leonardoAB1/smoke_detector_camera/docs/inform/media/markiv/simulacion_base_.png

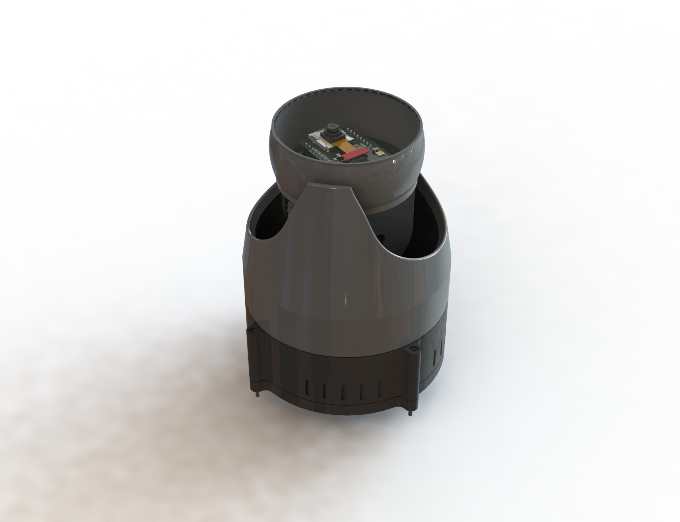
docs/inform/media/markiv/simulacion_base_.png
