leonardoAB1/smoke_detector_camera/docs/inform/media/vista_explosionada_mark3.png

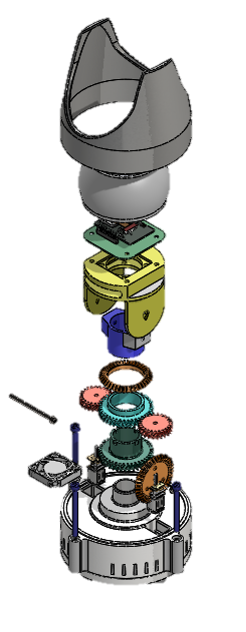
docs/inform/media/vista_explosionada_mark3.png
