leonardoAB1/smoke_detector_camera/cad/mark_02/components/LightSensor.step

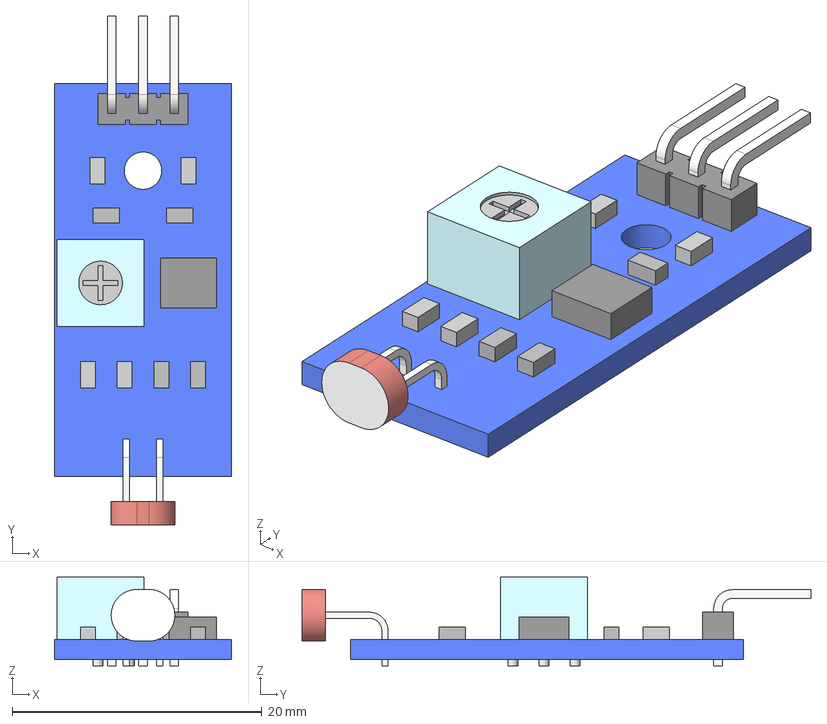
[picture p47: CAD file, 2023-06-11]
cad/mark_02/components/LightSensor.step
14.2 x 40.8 x 7.10 mm
