leonardoAB1/smoke_detector_camera/cad/mark_02/components/MQ135.SLDPRT

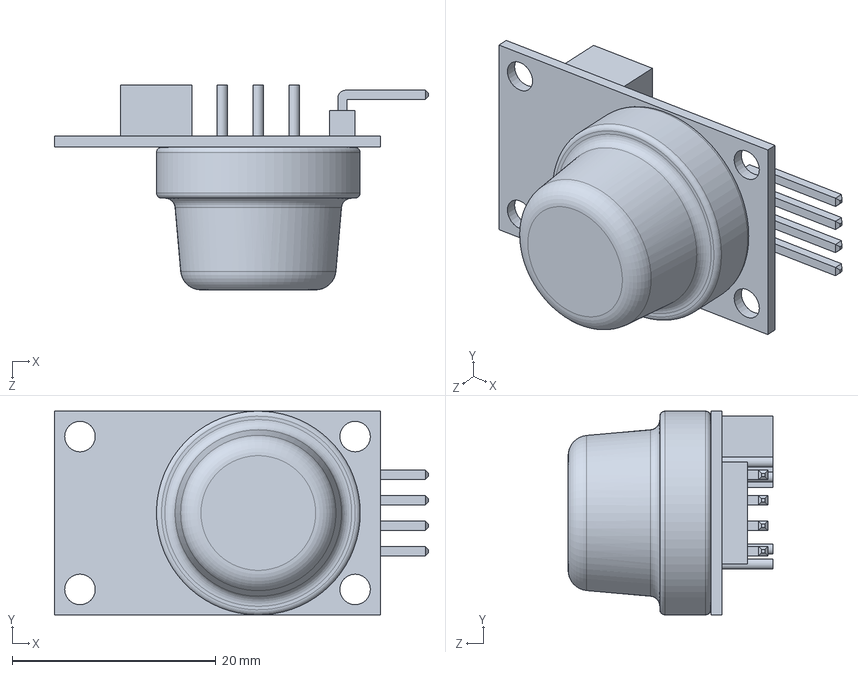
[picture p48: CAD file, 2023-06-11]
cad/mark_02/components/MQ135.SLDPRT
36.7 x 20.0 x 20.1 mm
