leonardoAB1/smoke_detector_camera/cad/mark_02/components/Li-Ion_Cell_Holder_BH_18650_A.SLDPRT

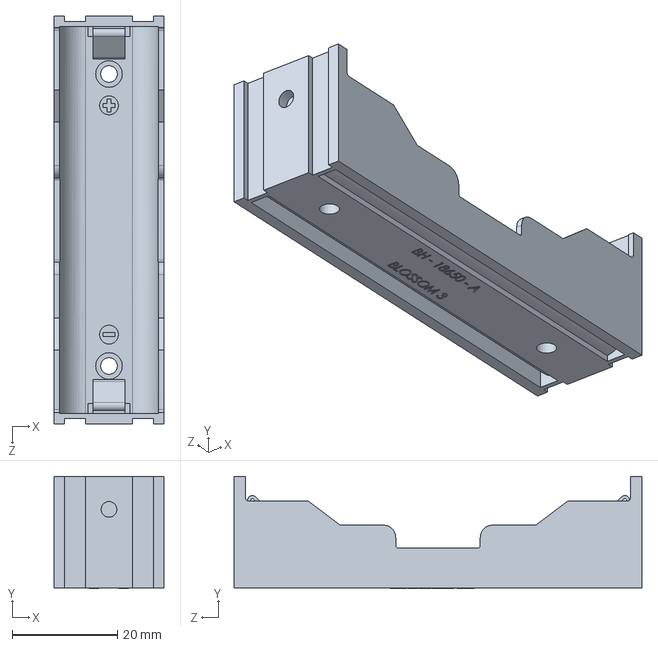
[picture p49: CAD file, 2023-06-11]
cad/mark_02/components/Li-Ion_Cell_Holder_BH_18650_A.SLDPRT
20.9 x 21.4 x 77.7 mm
