leonardoAB1/smoke_detector_camera/cad/mark_02/components/PIR-HC_SR501.SLDPRT

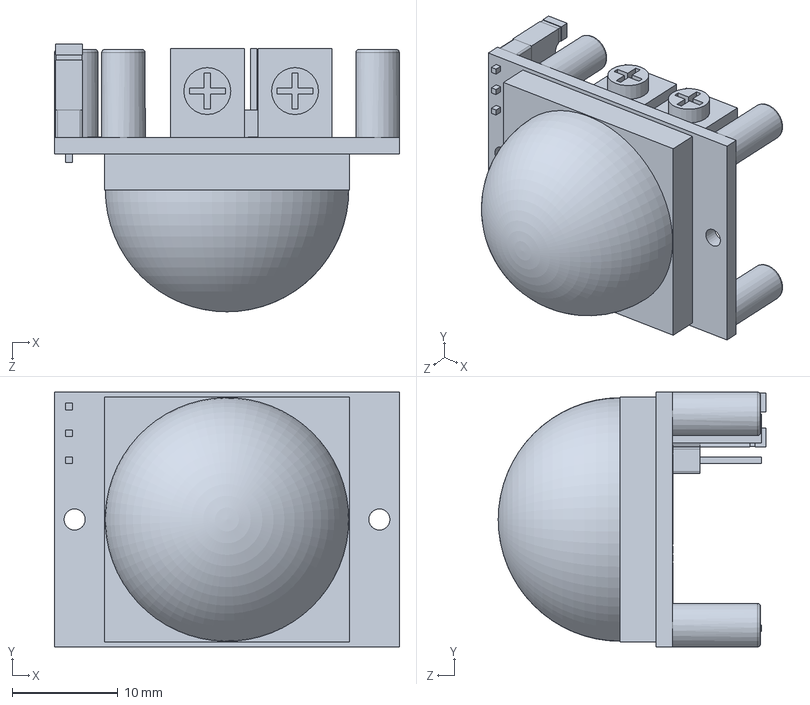
[picture p50: CAD file, 2023-06-11]
cad/mark_02/components/PIR-HC_SR501.SLDPRT
32.6 x 24.1 x 25.3 mm
