leonardoAB1/smoke_detector_camera/cad/mark_02/components/MG995.SLDPRT

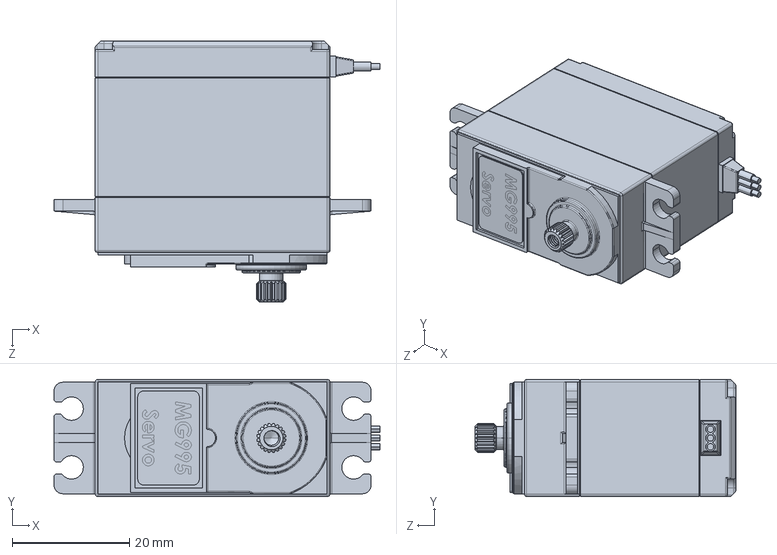
[picture p51: CAD file, 2023-06-11]
cad/mark_02/components/MG995.SLDPRT
55.5 x 20.0 x 44.5 mm
