leonardoAB1/smoke_detector_camera/cad/mark_02/components/Microservo horn.SLDPRT

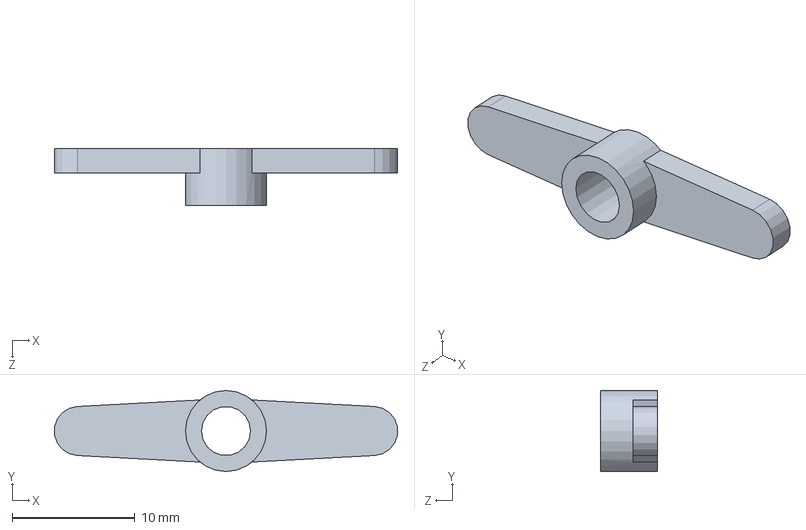
[picture p52: CAD file, 2023-06-11]
cad/mark_02/components/Microservo horn.SLDPRT
27.9 x 6.60 x 4.68 mm
