leonardoAB1/smoke_detector_camera/cad/mark_02/components/ELCOM EMI-21 INLET 16 amps.STEP

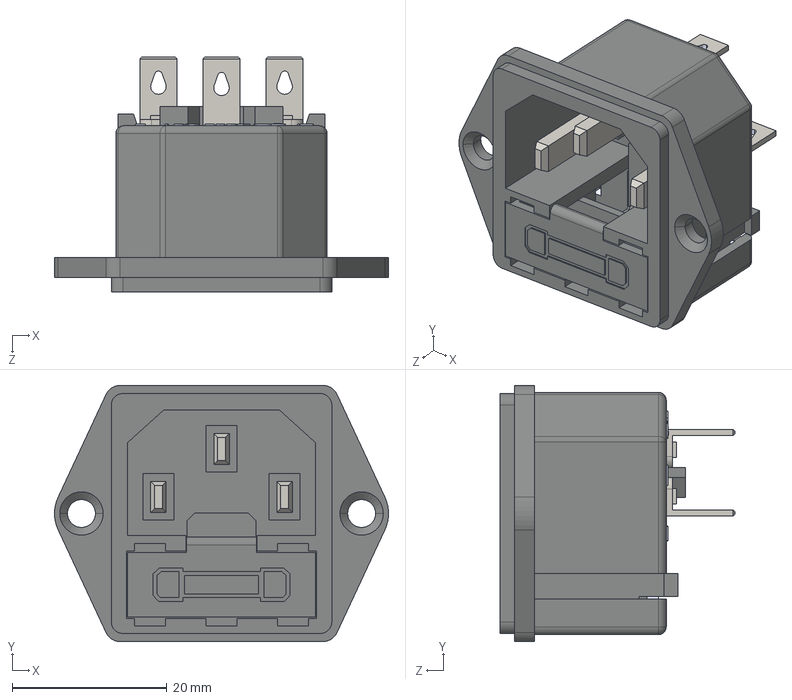
[picture p53: CAD file, 2023-06-11]
cad/mark_02/components/ELCOM EMI-21 INLET 16 amps.STEP
43.2 x 33.1 x 30.4 mm
ELCOM EMI-21 INLET
ELCOM EMI-21 INLET tray
