leonardoAB1/smoke_detector_camera/cad/mark_02/components/Switch.SLDPRT

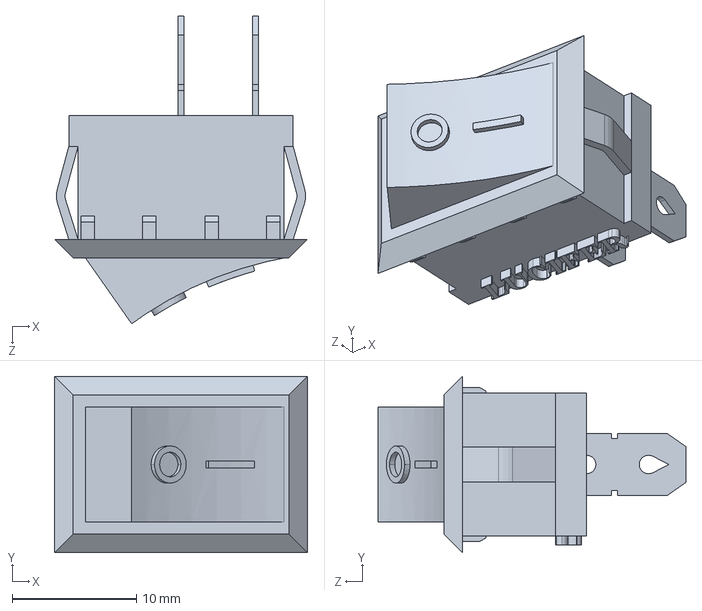
[picture p54: CAD file, 2023-06-09]
cad/mark_02/components/Switch.SLDPRT
20.4 x 14.2 x 24.8 mm
