leonardoAB1/smoke_detector_camera/cad/mark_02/components/MG90S.SLDPRT

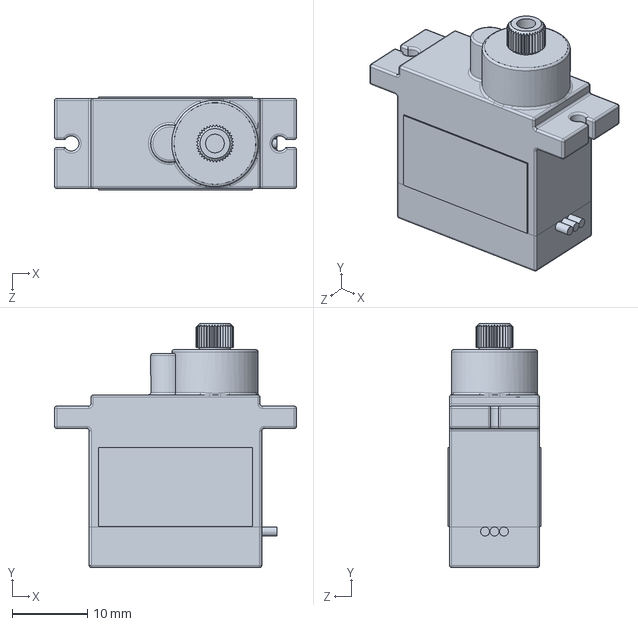
[picture p55: CAD file, 2023-06-02]
cad/mark_02/components/MG90S.SLDPRT
32.2 x 32.5 x 12.4 mm
