leonardoAB1/smoke_detector_camera/src/device/main/src/http_handlers/http_handlers.c

/*******************************************************************************
 * @file        http_handlers.c
 * @author      Leonardo Acha Boiano
 * @date        7 Jun 2023
 * 
 * @note        This code is written in C and is used on an ESP32-CAM development board.
 *
 *******************************************************************************/

#include "../http_handlers/http_handlers.h"

// HTTP request handler for getting a single image base64 encoded
esp_err_t image_base64_httpd_handler(httpd_req_t *req)
{
    // Authenticate the user
    authenticatedUserRole = authenticateUser(req);

    if (authenticatedUserRole != ROLE_USER && authenticatedUserRole != ROLE_ADMIN) {
        httpd_resp_send_err(req, HTTPD_401_UNAUTHORIZED, "Unauthorized");
        return ESP_OK;
    }

    camera_fb_t *fb = esp_camera_fb_get();
    if (!fb) {
        ESP_LOGE(CAMERA_TAG, "Camera capture failed");
        httpd_resp_send_err(req, HTTPD_500_INTERNAL_SERVER_ERROR, "Internal Server Error");
        return ESP_FAIL;
    }

    // Set the content type header
    httpd_resp_set_type(req, "image/jpeg");

    // Calculate the size of the base64-encoded data
    size_t encoded_len = (fb->len + 2) / 3 * 4;

    char *encoded_data = (char *)malloc(encoded_len);
    if (!encoded_data) {
        ESP_LOGE(CAMERA_TAG, "Memory allocation failed");
        httpd_resp_send_err(req, HTTPD_500_INTERNAL_SERVER_ERROR, "Internal Server Error");
        esp_camera_fb_return(fb);
        return ESP_FAIL;
    }

    // Encode the image data using base64
    size_t encoded_data_len = encoded_len;
    int ret = base64_encode((const unsigned char *)fb->buf, fb->len, encoded_data, &encoded_data_len);
    if (ret != 0) {
        ESP_LOGE(CAMERA_TAG, "Base64 encoding failed. Error code: %d", ret);
        ESP_LOGE(CAMERA_TAG, "Encoded data length: %d", encoded_data_len);
        httpd_resp_send_err(req, HTTPD_500_INTERNAL_SERVER_ERROR, "Internal Server Error");
        free(encoded_data);
        esp_camera_fb_return(fb);
        return ESP_FAIL;
    }

    // Send the encoded image data as the response
    httpd_resp_send(req, encoded_data, encoded_data_len);

    // Cleanup
    free(encoded_data);
    esp_camera_fb_return(fb);

    return ESP_OK;
}

// HTTP request handler for getting a single image
esp_err_t image_httpd_handler(httpd_req_t *req)
{
    // Authenticate the user
    authenticatedUserRole = authenticateUser(req);

    if (authenticatedUserRole != ROLE_USER && authenticatedUserRole != ROLE_ADMIN) {
        httpd_resp_send_err(req, HTTPD_401_UNAUTHORIZED, "Unauthorized");
        return ESP_OK;
    }

    camera_fb_t *fb = esp_camera_fb_get();
    if (!fb) {
        ESP_LOGE(CAMERA_TAG, "Camera capture failed");
        httpd_resp_send_err(req, HTTPD_500_INTERNAL_SERVER_ERROR, "Internal Server Error");
        return ESP_FAIL;
    }

    // Set the content type header
    httpd_resp_set_type(req, "image/jpeg");

    // Send the image data
    httpd_resp_send(req, (const char *)fb->buf, fb->len);

    esp_camera_fb_return(fb);
    return ESP_OK;
}

// HTTP request handler for getting the camera status
esp_err_t status_httpd_handler(httpd_req_t *req)
{
    // Authenticate the user
    authenticatedUserRole = authenticateUser(req);

    if (authenticatedUserRole != ROLE_USER && authenticatedUserRole != ROLE_ADMIN) {
        httpd_resp_send_err(req, HTTPD_401_UNAUTHORIZED, "Unauthorized");
        return ESP_OK;
    }

    cJSON *root = cJSON_CreateObject();
    cJSON_AddStringToObject(root, "status", "online");

    char *response = cJSON_Print(root);

    httpd_resp_set_type(req, "application/json");
    httpd_resp_send(req, response, strlen(response));

    cJSON_Delete(root);
    free(response);

    return ESP_OK;
}

// HTTP request handler for admin functionality
esp_err_t admin_httpd_handler(httpd_req_t *req)
{
    // Authenticate the user
    authenticatedUserRole = authenticateUser(req);

    if (authenticatedUserRole != ROLE_ADMIN) {
        httpd_resp_send_err(req, HTTPD_401_UNAUTHORIZED, "Unauthorized");
        return ESP_OK;
    }

    // Check if the request method is POST
    if (req->method != HTTP_POST) {
        httpd_resp_send_err(req, HTTPD_405_METHOD_NOT_ALLOWED, "Method Not Allowed");
        return ESP_OK;
    }

    // Get the content length
    char content_length_str[16];
    if (httpd_req_get_hdr_value_str(req, "Content-Length", content_length_str, sizeof(content_length_str)) != ESP_OK) {
        httpd_resp_send_err(req, HTTPD_400_BAD_REQUEST, "Bad Request");
        return ESP_OK;
    }

    size_t content_len = atoi(content_length_str);

    // Read the request content data
    char *content = malloc(content_len + 1);
    if (!content) {
        httpd_resp_send_err(req, HTTPD_500_INTERNAL_SERVER_ERROR, "Internal Server Error");
        return ESP_OK;
    }

    int ret = httpd_req_recv(req, content, content_len);
    if (ret <= 0) {
        free(content);
        httpd_resp_send_err(req, HTTPD_400_BAD_REQUEST, "Bad Request");
        return ESP_OK;
    }

    content[ret] = '\0'; // Null-terminate the content

    // Parse the JSON content
    cJSON *json = cJSON_Parse(content);
    if (!json) {
        free(content);
        httpd_resp_send_err(req, HTTPD_400_BAD_REQUEST, "Invalid JSON");
        return ESP_OK;
    }

    // Get the value from the JSON object
    cJSON *valueObj = cJSON_GetObjectItem(json, "value");
    if (!valueObj || !cJSON_IsNumber(valueObj)) {
        cJSON_Delete(json);
        free(content);
        httpd_resp_send_err(req, HTTPD_400_BAD_REQUEST, "Invalid JSON");
        return ESP_OK;
    }

    int value = valueObj->valueint;

    // Log the updated value
    ESP_LOGI(ADMIN_TAG, "Value updated: %d", value);

    // Process the value (e.g., perform admin action)
    // ...

    // Cleanup
    cJSON_Delete(json);
    free(content);

    // Send a response
    httpd_resp_set_type(req, "text/plain");
    httpd_resp_send(req, "Value updated successfully", -1);

    return ESP_OK;
}

// Handler for the API endpoint to control the motors
esp_err_t handle_set_motor_angle(httpd_req_t *req) {
    // Authenticate the user and check if the role is admin
    authenticatedUserRole = authenticateUser(req);
    if (authenticatedUserRole != ROLE_ADMIN) {
        // Return an error response indicating insufficient permissions
        httpd_resp_send_err(req, HTTPD_401_UNAUTHORIZED, "Insufficient permissions");
        return ESP_OK;
    }

    // TODO:Extract the desired motor angles from the request parameters
    // Example: int angle1 = extract_angle_from_request(req, "angle1");
    //          int angle2 = extract_angle_from_request(req, "angle2");
    
    // Call the move_motors_custom() function to move the motors accordingly
    // Example: move_motors_custom(angle1, angle2);
    
    // Return a success response indicating the motors have been moved
    httpd_resp_sendstr(req, "Motors moved successfully");
    return ESP_OK;
}

// Handler for the API endpoint to get the motor current position
esp_err_t handle_get_motor_angle(httpd_req_t *req)
{
    // Authenticate the user and check if the role is admin or user
    authenticatedUserRole = authenticateUser(req);
    if (authenticatedUserRole == ROLE_UNKNOWN)
    {
        // Return an error response indicating unauthorized access
        httpd_resp_send_err(req, HTTPD_401_UNAUTHORIZED, "Unauthorized access");
        return ESP_OK;
    }

    // Get the motor number from the request header
    int motorNumber = -1;
    size_t motorHeaderLen = httpd_req_get_hdr_value_len(req, "Motor-Number");
    if (motorHeaderLen > 0)
    {
        char *motorHeader = malloc(motorHeaderLen + 1);
        httpd_req_get_hdr_value_str(req, "Motor-Number", motorHeader, motorHeaderLen + 1);
        motorNumber = atoi(motorHeader);
        free(motorHeader);
    }

    // Check the motor number and retrieve the corresponding motor angle
    float motorAngle = -1.0;
    if (motorNumber == 1)
    {
        motorAngle = get_motor_angle(&motor1);
    }
    else if (motorNumber == 2)
    {
        motorAngle = get_motor_angle(&motor2);
    }
    else
    {
        // Return an error response for an invalid motor number
        httpd_resp_send_err(req, HTTPD_400_BAD_REQUEST, "Invalid motor number");
        return ESP_OK;
    }

    // Create a JSON response payload with the motor angle
    cJSON *json = cJSON_CreateObject();
    cJSON_AddNumberToObject(json, "motor_angle", motorAngle);
    char *payload = cJSON_PrintUnformatted(json);
    cJSON_Delete(json);

    // Set the Content-Type header to application/json
    httpd_resp_set_type(req, "application/json");

    // Send the JSON response payload
    httpd_resp_send(req, payload, strlen(payload));

    // Free the allocated JSON payload
    free(payload);

    return ESP_OK;
}

// Handler for the API endpoint to control the LEDs
esp_err_t handle_set_ldr(httpd_req_t *req) {
    // Authenticate the user and check if the role is admin
    authenticatedUserRole = authenticateUser(req);
    if (authenticatedUserRole != ROLE_ADMIN) {
        // Return an error response indicating insufficient permissions
        httpd_resp_send_err(req, HTTPD_401_UNAUTHORIZED, "Insufficient permissions");
        return ESP_OK;
    }

    // TODO:Extract the desired LED state from the request parameters
    // Example: bool ledState = extract_led_state_from_request(req, "ledState");
    
    // Set the LED GPIO pin state accordingly
    // Example: gpio_set_level(GPIO_LEDS, ledState);
    
    // Return a success response indicating the LEDs have been controlled
    httpd_resp_sendstr(req, "LDR controlled successfully");
    return ESP_OK;
}

// Handler for the API endpoint to get the LEDs current state
esp_err_t handle_get_ldr(httpd_req_t *req){
    // Authenticate the user and check if the role is admin or user
    authenticatedUserRole = authenticateUser(req);
    if (authenticatedUserRole == ROLE_UNKNOWN) {
        // Return an error response indicating unauthorized access
        httpd_resp_send_err(req, HTTPD_401_UNAUTHORIZED, "Unauthorized access");
        return ESP_OK;
    }

    // Prepare the response JSON
    cJSON *root = cJSON_CreateObject();
    cJSON_AddStringToObject(root, "state", getLdrState() == 0 ? "0" : "1");

    char *response = cJSON_Print(root);

    // Set the response headers and send the response
    httpd_resp_set_type(req, "application/json");
    httpd_resp_send(req, response, strlen(response));

    // Clean up
    cJSON_Delete(root);
    free(response);

    return ESP_OK;
}



// Handler for the API endpoint to control the LEDs
esp_err_t handle_set_led(httpd_req_t *req) {
    // Authenticate the user and check if the role is admin
    authenticatedUserRole = authenticateUser(req);
    if (authenticatedUserRole != ROLE_ADMIN) {
        // Return an error response indicating insufficient permissions
        httpd_resp_send_err(req, HTTPD_401_UNAUTHORIZED, "Insufficient permissions");
        return ESP_OK;
    }

    // TODO:Extract the desired LED state from the request parameters
    // Example: bool ledState = extract_led_state_from_request(req, "ledState");
    
    // Set the LED GPIO pin state accordingly
    // Example: gpio_set_level(GPIO_LEDS, ledState);
    
    // Return a success response indicating the LEDs have been controlled
    httpd_resp_sendstr(req, "LEDs controlled successfully");
    return ESP_OK;
}

// Handler for the API endpoint to get the LEDs current state
esp_err_t handle_get_led(httpd_req_t *req){
    // Authenticate the user and check if the role is admin or user
    authenticatedUserRole = authenticateUser(req);
    if (authenticatedUserRole == ROLE_UNKNOWN) {
        // Return an error response indicating unauthorized access
        httpd_resp_send_err(req, HTTPD_401_UNAUTHORIZED, "Unauthorized access");
        return ESP_OK;
    }

    // Prepare the response JSON
    cJSON *root = cJSON_CreateObject();
    cJSON_AddStringToObject(root, "state", getLedState() == 0 ? "0" : "1");

    char *response = cJSON_Print(root);

    // Set the response headers and send the response
    httpd_resp_set_type(req, "application/json");
    httpd_resp_send(req, response, strlen(response));

    // Clean up
    cJSON_Delete(root);
    free(response);

    return ESP_OK;
}

// Handler for the API endpoint to set the smoke sensor test variable
// Implemented in order to test system behavior
esp_err_t handle_set_smoke_sensor(httpd_req_t *req){
    // Authenticate the user and check if the role is admin
    authenticatedUserRole = authenticateUser(req);
    if (authenticatedUserRole != ROLE_ADMIN) {
        // Return an error response indicating insufficient permissions
        httpd_resp_send_err(req, HTTPD_401_UNAUTHORIZED, "Insufficient permissions");
        return ESP_OK;
    }

    //TODO: Implement handler

    return ESP_OK;
}

// Handler for the API endpoint to access the smoke sensor data
esp_err_t handle_get_smoke_sensor(httpd_req_t *req) {
    // Authenticate the user and check if the role is admin or user
    authenticatedUserRole = authenticateUser(req);
    if (authenticatedUserRole == ROLE_UNKNOWN) {
        // Return an error response indicating unauthorized access
        httpd_resp_send_err(req, HTTPD_401_UNAUTHORIZED, "Unauthorized access");
        return ESP_OK;
    }
    
    // Return the JSON response
    cJSON *root = cJSON_CreateObject();
    cJSON_AddStringToObject(root, "state", getSmokeSensorState() == 0 ? "0" : "1");

    char *response = cJSON_Print(root);

    // Set the response headers and send the response
    httpd_resp_set_type(req, "application/json");
    httpd_resp_send(req, response, strlen(response));

    // Clean up
    cJSON_Delete(root);
    free(response);

    return ESP_OK;
}

/********************************* END OF FILE ********************************/
/******************************************************************************/
