leonardoAB1/smoke_detector_camera/src/device/main/src/http_handlers/http_handlers.h

/*******************************************************************************
 * @file        http_handlers.h
 * @brief       Header file containing declarations of HTTP request handlers.
 * @author      Leonardo Acha Boiano
 * @date        7 Jun 2023
 * 
 * @note        This code is written in C and is used on an ESP32-CAM development board.
 *
 *******************************************************************************/

#ifndef HTTP_HANDLERS_H
#define HTTP_HANDLERS_H

#include <stdio.h>
#include <stdlib.h>
#include <string.h>
#include <esp_log.h>
#include <esp_camera.h>
#include <cJSON.h>
#include <esp_http_server.h>

#include "../logging/logging_utils.h"
#include "../user_roles/user_roles.h"
#include "../base64/base64_utils.h"
#include "../camera/camera_pins.h"
#include "../gpio_interrupts/gpio_interrupts.h"
#include "../gpio_state/gpio_state.h"
#include "../motor_control/motor_control.h"

/**
 * @brief       The authenticated user role.
 * @note        This variable is defined in main.c.
 */
extern UserRole authenticatedUserRole;

/**
 * @brief       HTTP request handler for getting a single image in base64 encoding.
 * @param[in]   req The HTTP request object.
 * @return      An esp_err_t indicating the success or failure of the operation.
 */
esp_err_t image_base64_httpd_handler(httpd_req_t *req);

/**
 * @brief       HTTP request handler for getting a single image.
 * @param[in]   req The HTTP request object.
 * @return      An esp_err_t indicating the success or failure of the operation.
 */
esp_err_t image_httpd_handler(httpd_req_t *req);

/**
 * @brief       HTTP request handler for getting the camera status.
 * @param[in]   req The HTTP request object.
 * @return      An esp_err_t indicating the success or failure of the operation.
 */
esp_err_t status_httpd_handler(httpd_req_t *req);

/**
 * @brief       HTTP request handler for admin functionality.
 * @param[in]   req The HTTP request object.
 * @return      An esp_err_t indicating the success or failure of the operation.
 */
esp_err_t admin_httpd_handler(httpd_req_t *req);

esp_err_t handle_set_motor_angle(httpd_req_t *req); //motor number and angle needed in header
esp_err_t handle_get_motor_angle(httpd_req_t *req);
esp_err_t handle_set_ldr(httpd_req_t *req);
esp_err_t handle_get_ldr(httpd_req_t *req);
esp_err_t handle_set_led(httpd_req_t *req);
esp_err_t handle_get_led(httpd_req_t *req);
esp_err_t handle_set_smoke_sensor(httpd_req_t *req);
esp_err_t handle_get_smoke_sensor(httpd_req_t *req);

extern Motor motor1;
extern Motor motor2;

#endif  // HTTP_HANDLERS_H

/********************************* END OF FILE ********************************/
/******************************************************************************/
