leonardoAB1/smoke_detector_camera/src/device/main/src/bt_utils/bt_utils.c

/*******************************************************************************
 * @file        bt_utils.c
 * @author      Leonardo Acha Boiano
 * @date        20 Jul 2023
 * 
 * @note        This code is written in C and is used on an ESP32-CAM development board.
 *
 *******************************************************************************/

#include "../bt_utils/bt_utils.h"

#if ENABLE_BT

static uint32_t connection_handle;

static const esp_spp_mode_t esp_spp_mode = ESP_SPP_MODE_CB;
static const bool esp_spp_enable_l2cap_ertm = true;

static struct timeval time_new, time_old;
static long data_num = 0;

static const esp_spp_sec_t sec_mask = ESP_SPP_SEC_AUTHENTICATE;
static const esp_spp_role_t role_slave = ESP_SPP_ROLE_SLAVE;

void bt_printf(const char *format, ...)
{
    // Check if the connection handle is valid
    if (connection_handle == NULL) {
        printf("Bluetooth connection handle is not valid. Cannot send data.\n");
        return;
    }

    // Create a buffer to hold the formatted string
    char buffer[BT_TX_BUFFER_SIZE];

    // Format the string using variable arguments
    va_list args;
    va_start(args, format);
    vsnprintf(buffer, sizeof(buffer), format, args);
    va_end(args);

    // Print the formatted string to the console for debugging (optional)
    //printf("Formatted string: %s", buffer);

    // Send the formatted string through Bluetooth
    esp_spp_write(connection_handle, strlen(buffer), (uint8_t *)buffer);
}

static char *bda2str(uint8_t * bda, char *str, size_t size)
{
    if (bda == NULL || str == NULL || size < 18) {
        return NULL;
    }

    uint8_t *p = bda;
    sprintf(str, "%02x:%02x:%02x:%02x:%02x:%02x",
            p[0], p[1], p[2], p[3], p[4], p[5]);
    return str;
}

static void print_speed(void)
{
    float time_old_s = time_old.tv_sec + time_old.tv_usec / 1000000.0;
    float time_new_s = time_new.tv_sec + time_new.tv_usec / 1000000.0;
    float time_interval = time_new_s - time_old_s;
    float speed = data_num * 8 / time_interval / 1000.0;
    ESP_LOGI(BT_TAG, "speed(%fs ~ %fs): %f kbit/s" , time_old_s, time_new_s, speed);
    data_num = 0;
    time_old.tv_sec = time_new.tv_sec;
    time_old.tv_usec = time_new.tv_usec;
}

static void esp_spp_cb(esp_spp_cb_event_t event, esp_spp_cb_param_t *param)
{
    char bda_str[18] = {0};

    switch (event) {
    case ESP_SPP_INIT_EVT:
        if (param->init.status == ESP_SPP_SUCCESS) {
            ESP_LOGI(BT_TAG, "ESP_SPP_INIT_EVT");
            esp_spp_start_srv(sec_mask, role_slave, 0, SPP_SERVER_NAME);
        } else {
            ESP_LOGE(BT_TAG, "ESP_SPP_INIT_EVT status:%d", param->init.status);
        }
        break;
        /*********************************************************************************************************/
    case ESP_SPP_DISCOVERY_COMP_EVT:
        ESP_LOGI(BT_TAG, "ESP_SPP_DISCOVERY_COMP_EVT");
        break;
        /*********************************************************************************************************/
    case ESP_SPP_OPEN_EVT:
        ESP_LOGI(BT_TAG, "ESP_SPP_OPEN_EVT");
        break;
        /*********************************************************************************************************/
    case ESP_SPP_CLOSE_EVT:
        ESP_LOGI(BT_TAG, "ESP_SPP_CLOSE_EVT status:%d handle:%"PRIu32" close_by_remote:%d", param->close.status,
                 param->close.handle, param->close.async);
        break;
        /*********************************************************************************************************/
    case ESP_SPP_START_EVT:
        if (param->start.status == ESP_SPP_SUCCESS) {
            ESP_LOGI(BT_TAG, "ESP_SPP_START_EVT handle:%"PRIu32" sec_id:%d scn:%d", param->start.handle, param->start.sec_id,
                     param->start.scn);
            esp_bt_dev_set_device_name(DEVICE_NAME);
            esp_bt_gap_set_scan_mode(ESP_BT_CONNECTABLE, ESP_BT_GENERAL_DISCOVERABLE);
        } else {
            ESP_LOGE(BT_TAG, "ESP_SPP_START_EVT status:%d", param->start.status);
        }
        break;
        /*********************************************************************************************************/
    case ESP_SPP_CL_INIT_EVT:
        ESP_LOGI(BT_TAG, "ESP_SPP_CL_INIT_EVT");
        break;
        /*********************************************************************************************************/
    case ESP_SPP_DATA_IND_EVT:
#if (SPP_SHOW_MODE == SPP_SHOW_DATA)
        /*
         * We only show the data in which the data length is less than 128 here. If you want to print the data and
         * the data rate is high, it is strongly recommended to process them in other lower priority application task
         * rather than in this callback directly. Since the printing takes too much time, it may stuck the Bluetooth
         * stack and also have a effect on the throughput!
         */
        ESP_LOGI(BT_TAG, "ESP_SPP_DATA_IND_EVT len:%d handle:%lu",
                 param->data_ind.len, param->data_ind.handle);
        if (param->data_ind.len < 128) {
            esp_log_buffer_hex("", param->data_ind.data, param->data_ind.len);
            //echo message
            //esp_spp_write(param->data_ind.handle, param->data_ind.len, param->data_ind.data);
            //bt_printf("This is a test message: %d, %s", 42, "Hello!");
            //bt_printf("This is another test message");
        }
        //if needed, here goes actions triggered by message received
#else
        gettimeofday(&time_new, NULL);
        data_num += param->data_ind.len;
        if (time_new.tv_sec - time_old.tv_sec >= 3) {
            print_speed();
        }
#endif /*SPP_SHOW_MODE == SPP_SHOW_DATA*/
        break;
        /*********************************************************************************************************/
    case ESP_SPP_CONG_EVT:
        ESP_LOGI(BT_TAG, "ESP_SPP_CONG_EVT");
        break;
        /*********************************************************************************************************/
    case ESP_SPP_WRITE_EVT:
        //ESP_LOGI(BT_TAG, "ESP_SPP_WRITE_EVT");
        break;
        /*********************************************************************************************************/
    case ESP_SPP_SRV_OPEN_EVT:
        //This event indicates that the SPP server has been opened, 
        //and the connection handle is provided as a parameter.
        // Store the connection handle for future reference
        connection_handle = param->srv_open.handle;
        ESP_LOGI(BT_TAG, "ESP_SPP_SRV_OPEN_EVT status:%d handle:%"PRIu32", rem_bda:[%s]", param->srv_open.status,
                 param->srv_open.handle, bda2str(param->srv_open.rem_bda, bda_str, sizeof(bda_str)));
        gettimeofday(&time_old, NULL);
        break;
        /*********************************************************************************************************/
    case ESP_SPP_SRV_STOP_EVT:
        ESP_LOGI(BT_TAG, "ESP_SPP_SRV_STOP_EVT");
        break;
        /*********************************************************************************************************/
    case ESP_SPP_UNINIT_EVT:
        ESP_LOGI(BT_TAG, "ESP_SPP_UNINIT_EVT");
        break;
        /*********************************************************************************************************/
    default:
        break;
        /*********************************************************************************************************/
    }
}

void esp_bt_gap_cb(esp_bt_gap_cb_event_t event, esp_bt_gap_cb_param_t *param)
{
    char bda_str[18] = {0};

    switch (event) {
    case ESP_BT_GAP_AUTH_CMPL_EVT:{
        if (param->auth_cmpl.stat == ESP_BT_STATUS_SUCCESS) {
            ESP_LOGI(BT_TAG, "authentication success: %s bda:[%s]", param->auth_cmpl.device_name,
                     bda2str(param->auth_cmpl.bda, bda_str, sizeof(bda_str)));
        } else {
            ESP_LOGE(BT_TAG, "authentication failed, status:%d", param->auth_cmpl.stat);
        }
        break;
    }
    case ESP_BT_GAP_PIN_REQ_EVT:{
        ESP_LOGI(BT_TAG, "ESP_BT_GAP_PIN_REQ_EVT min_16_digit:%d", param->pin_req.min_16_digit);
        if (param->pin_req.min_16_digit) {
            ESP_LOGI(BT_TAG, "Input pin code: 0000 0000 0000 0000");
            esp_bt_pin_code_t pin_code = {0};
            esp_bt_gap_pin_reply(param->pin_req.bda, true, 16, pin_code);
        } else {
            ESP_LOGI(BT_TAG, "Input pin code: 1234");
            esp_bt_pin_code_t pin_code;
            pin_code[0] = '1';
            pin_code[1] = '2';
            pin_code[2] = '3';
            pin_code[3] = '4';
            esp_bt_gap_pin_reply(param->pin_req.bda, true, 4, pin_code);
        }
        break;
    }

#if (CONFIG_BT_SSP_ENABLED == true)
    case ESP_BT_GAP_CFM_REQ_EVT:
        ESP_LOGI(BT_TAG, "ESP_BT_GAP_CFM_REQ_EVT Please compare the numeric value: %"PRIu32, param->cfm_req.num_val);
        esp_bt_gap_ssp_confirm_reply(param->cfm_req.bda, true);
        break;
    case ESP_BT_GAP_KEY_NOTIF_EVT:
        ESP_LOGI(BT_TAG, "ESP_BT_GAP_KEY_NOTIF_EVT passkey:%"PRIu32, param->key_notif.passkey);
        break;
    case ESP_BT_GAP_KEY_REQ_EVT:
        ESP_LOGI(BT_TAG, "ESP_BT_GAP_KEY_REQ_EVT Please enter passkey!");
        break;
#endif

    case ESP_BT_GAP_MODE_CHG_EVT:
        ESP_LOGI(BT_TAG, "ESP_BT_GAP_MODE_CHG_EVT mode:%d bda:[%s]", param->mode_chg.mode,
                 bda2str(param->mode_chg.bda, bda_str, sizeof(bda_str)));
        break;

    default: {
        ESP_LOGI(BT_TAG, "event: %d", event);
        break;
    }
    }
    return;
}

void init_bluetooth(esp_err_t ret){
    char bda_str[18] = {0};

    if (ret == ESP_ERR_NVS_NO_FREE_PAGES || ret == ESP_ERR_NVS_NEW_VERSION_FOUND) {
        ESP_ERROR_CHECK(nvs_flash_erase());
        ret = nvs_flash_init();
    }
    ESP_ERROR_CHECK( ret );

    ESP_ERROR_CHECK(esp_bt_controller_mem_release(ESP_BT_MODE_BLE));

    esp_bt_controller_config_t bt_cfg = BT_CONTROLLER_INIT_CONFIG_DEFAULT();
    if ((ret = esp_bt_controller_init(&bt_cfg)) != ESP_OK) {
        ESP_LOGE(BT_TAG, "%s initialize controller failed: %s\n", __func__, esp_err_to_name(ret));
        return;
    }

    if ((ret = esp_bt_controller_enable(ESP_BT_MODE_CLASSIC_BT)) != ESP_OK) {
        ESP_LOGE(BT_TAG, "%s enable controller failed: %s\n", __func__, esp_err_to_name(ret));
        return;
    }

    if ((ret = esp_bluedroid_init()) != ESP_OK) {
        ESP_LOGE(BT_TAG, "%s initialize bluedroid failed: %s\n", __func__, esp_err_to_name(ret));
        return;
    }

    if ((ret = esp_bluedroid_enable()) != ESP_OK) {
        ESP_LOGE(BT_TAG, "%s enable bluedroid failed: %s\n", __func__, esp_err_to_name(ret));
        return;
    }

    if ((ret = esp_bt_gap_register_callback(esp_bt_gap_cb)) != ESP_OK) {
        ESP_LOGE(BT_TAG, "%s gap register failed: %s\n", __func__, esp_err_to_name(ret));
        return;
    }

    if ((ret = esp_spp_register_callback(esp_spp_cb)) != ESP_OK) {
        ESP_LOGE(BT_TAG, "%s spp register failed: %s\n", __func__, esp_err_to_name(ret));
        return;
    }

    esp_spp_cfg_t bt_spp_cfg = {
        .mode = esp_spp_mode,
        .enable_l2cap_ertm = esp_spp_enable_l2cap_ertm,
        .tx_buffer_size = 0, /* Only used for ESP_SPP_MODE_VFS mode */
    };
    if ((ret = esp_spp_enhanced_init(&bt_spp_cfg)) != ESP_OK) {
        ESP_LOGE(BT_TAG, "%s spp init failed: %s\n", __func__, esp_err_to_name(ret));
        return;
    }

#if (CONFIG_BT_SSP_ENABLED == true)
    /* Set default parameters for Secure Simple Pairing */
    esp_bt_sp_param_t param_type = ESP_BT_SP_IOCAP_MODE;
    esp_bt_io_cap_t iocap = ESP_BT_IO_CAP_IO;
    esp_bt_gap_set_security_param(param_type, &iocap, sizeof(uint8_t));
#endif

    /*
     * Set default parameters for Legacy Pairing
     * Use variable pin, input pin code when pairing
     */
    esp_bt_pin_type_t pin_type = ESP_BT_PIN_TYPE_VARIABLE;
    esp_bt_pin_code_t pin_code;
    esp_bt_gap_set_pin(pin_type, 0, pin_code);

    ESP_LOGI(BT_TAG, "Own address:[%s]", bda2str((uint8_t *)esp_bt_dev_get_address(), bda_str, sizeof(bda_str)));
}

#endif /* ENABLE_BT */

/********************************* END OF FILE ********************************/
/******************************************************************************/
