leonardoAB1/smoke_detector_camera/src/device/main/src/camera/camera_utils.c

/*******************************************************************************
 * @file        camera_utils.c
 * @author      Leonardo Acha Boiano
 * @date        7 Jun 2023
 * 
 * @note        This code is written in C and is used on an ESP32-CAM development board.
 *
 *******************************************************************************/

#include "../camera/camera_utils.h"

// Function to initialize the camera
esp_err_t init_camera(void)
{
    // Camera configuration structure
    camera_config_t camera_config = {
        // Camera pin configurations
        .pin_pwdn  = CAM_PIN_PWDN,
        .pin_reset = CAM_PIN_RESET,
        .pin_xclk = CAM_PIN_XCLK,
        .pin_sscb_sda = CAM_PIN_SIOD, 
        .pin_sscb_scl = CAM_PIN_SIOC,
        .pin_d7 = CAM_PIN_D7,
        .pin_d6 = CAM_PIN_D6,
        .pin_d5 = CAM_PIN_D5,
        .pin_d4 = CAM_PIN_D4,
        .pin_d3 = CAM_PIN_D3,
        .pin_d2 = CAM_PIN_D2,
        .pin_d1 = CAM_PIN_D1,
        .pin_d0 = CAM_PIN_D0,
        .pin_vsync = CAM_PIN_VSYNC,
        .pin_href = CAM_PIN_HREF,
        .pin_pclk = CAM_PIN_PCLK,

        // Camera configuration parameters
        .xclk_freq_hz = CONFIG_XCLK_FREQ,
        .ledc_timer = LEDC_TIMER_0,
        .ledc_channel = LEDC_CHANNEL_0,
        .pixel_format = PIXFORMAT_JPEG,
        .frame_size = FRAMESIZE_VGA,
        .jpeg_quality = 10,
        .fb_count = 1,
        .grab_mode = CAMERA_GRAB_WHEN_EMPTY // Sets when buffers should be filled
    };

    esp_err_t err = esp_camera_init(&camera_config);
    if (err != ESP_OK)
    {
        return err;
    }
    return ESP_OK;
}


/********************************* END OF FILE ********************************/
/******************************************************************************/
